PDXostc/canfw/hardware/Project Shares/V1.01 back.png

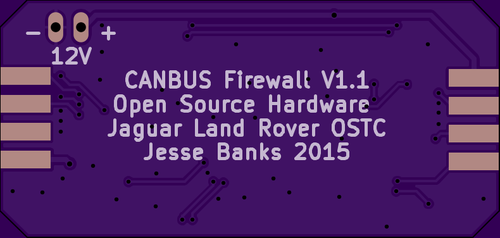
hardware/Project Shares/V1.01 back.png
