PDXostc/canfw/hardware/Project Shares/V1.11 Order Price.PNG

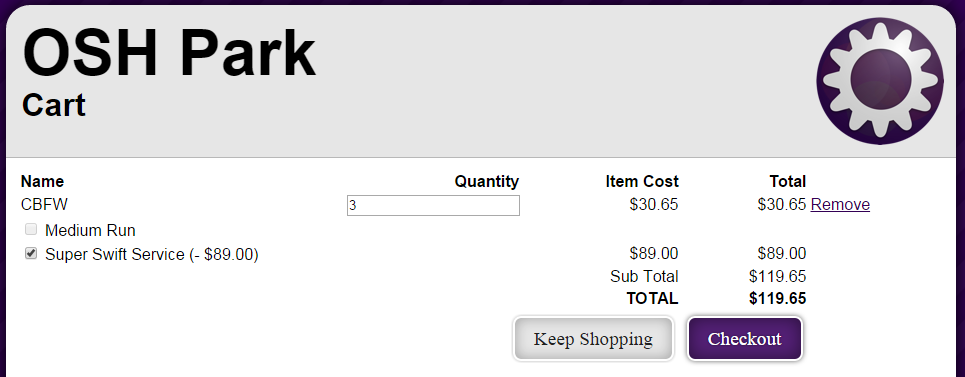
hardware/Project Shares/V1.11 Order Price.PNG
